Pablo-Ortiz-Lopez/ClimateController/electronics/board_back.jpg

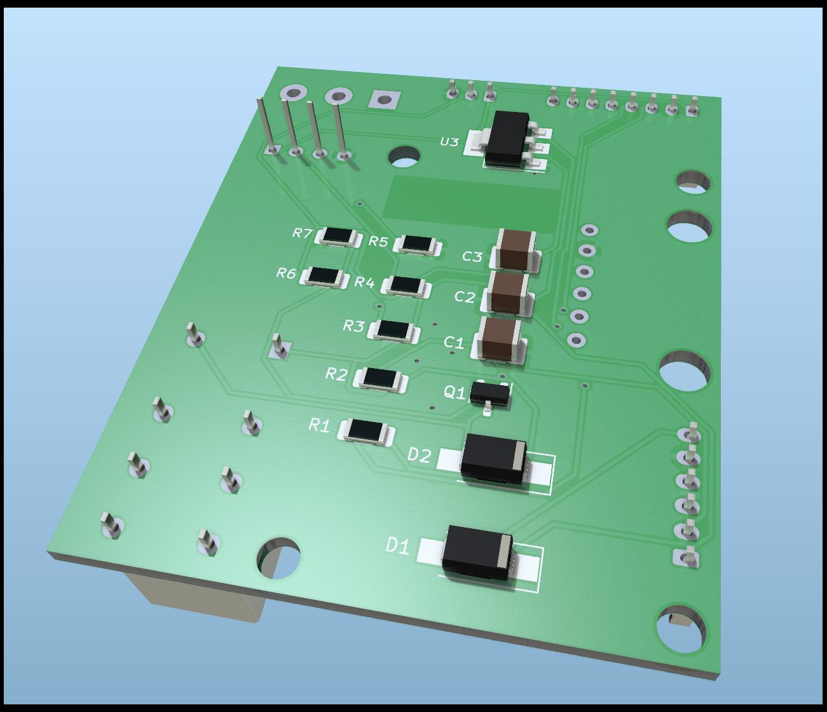
electronics/board_back.jpg
