Pablo-Ortiz-Lopez/ClimateController/electronics/board_front.jpg

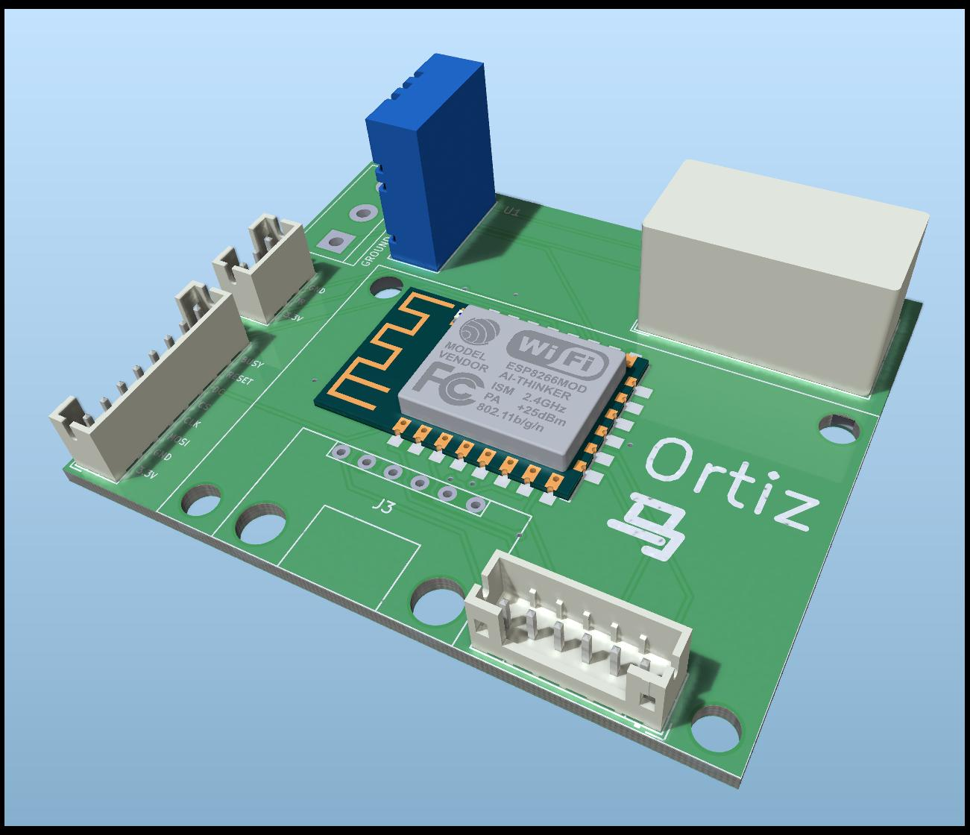
electronics/board_front.jpg
